LiuZSChina/OPSX/Sonnar/Body_controller/Rev1/3D/机身壳.STEP

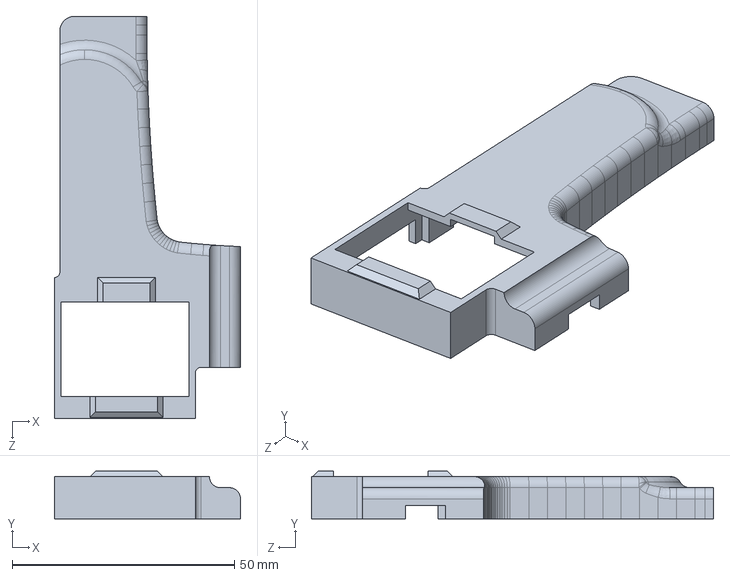
[picture p16: CAD file, 2023-06-15]
Sonnar/Body_controller/Rev1/3D/机身壳.STEP
41.8 x 10.7 x 90.5 mm
