LiuZSChina/OPSX/Sonnar/Body_controller/Rev1/3D/oled.SLDPRT

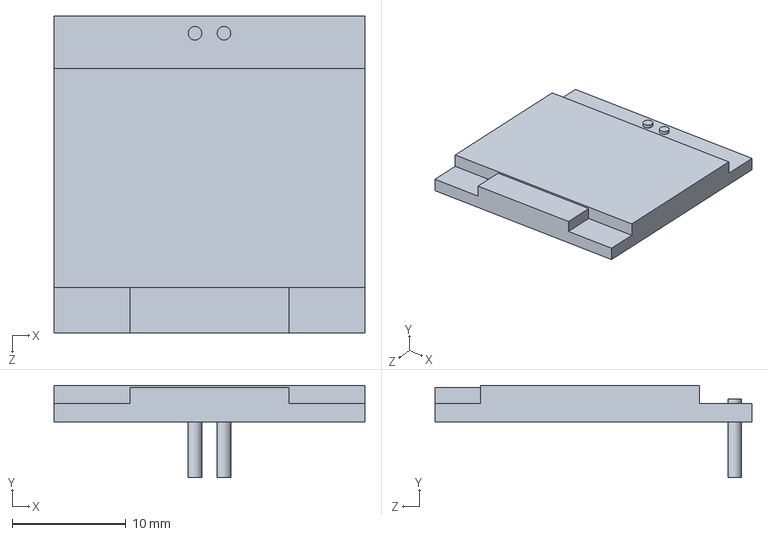
[picture p17: CAD file, 2023-05-23]
Sonnar/Body_controller/Rev1/3D/oled.SLDPRT
27.3 x 8.10 x 27.8 mm
