LiuZSChina/OPSX/Sonnar/Body_controller/Rev1/3D/rot_th.stl

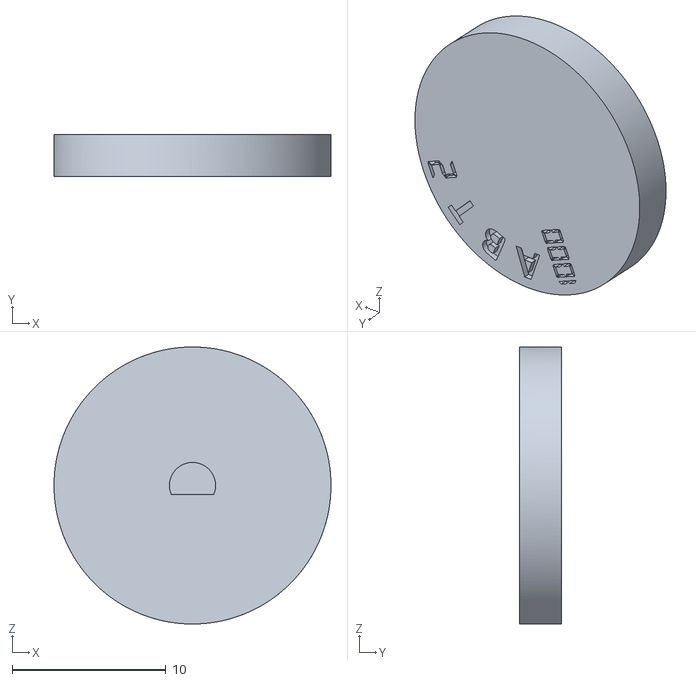
[picture p18: CAD file, 2023-05-20]
Sonnar/Body_controller/Rev1/3D/rot_th.stl
18.0 x 2.70 x 18.0
